carmamo/Avionics-FYCUS/Hardware/KiCAD_Libs/RM-VT02/3D/RM-VT02.stp

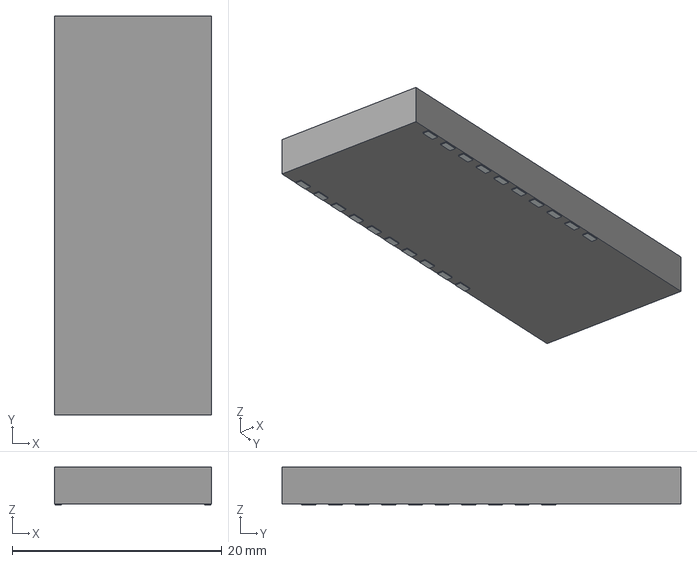
[picture p23: CAD file, 2023-10-23]
Hardware/KiCAD_Libs/RM-VT02/3D/RM-VT02.stp
15.0 x 38.0 x 3.60 mm
Pins
