carmamo/Avionics-FYCUS/Hardware/KiCAD_Libs/RQ3G100GNTB/3D/RQ3G100GNTB.stp

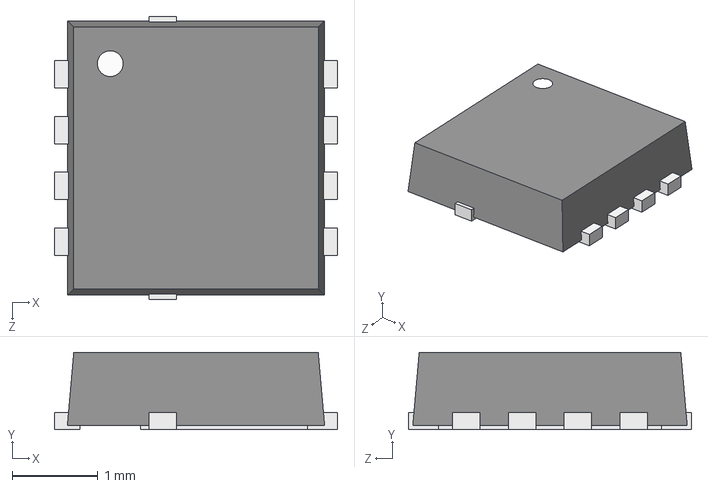
[picture p24: CAD file, 2023-10-23]
Hardware/KiCAD_Libs/RQ3G100GNTB/3D/RQ3G100GNTB.stp
3.30 x 0.9 x 3.30 mm
