carmamo/Avionics-FYCUS/Hardware/KiCAD_Libs/SSW-120-03-G-D/3D/SSW-120-03-G-D.stp

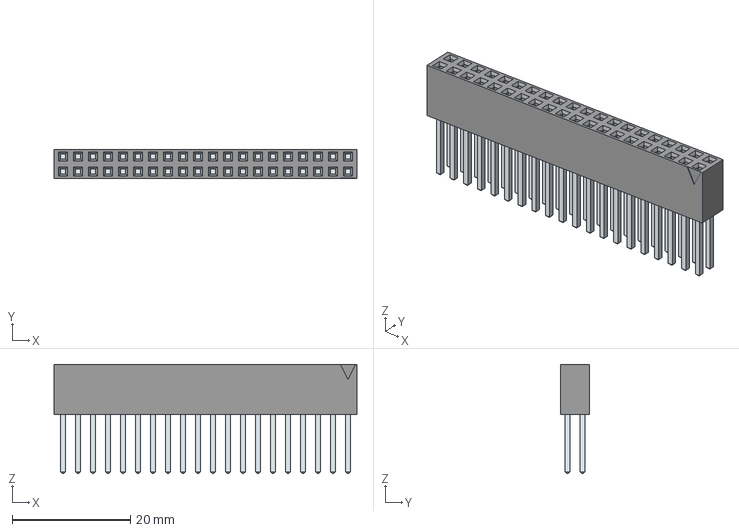
[picture p25: CAD file, 2023-10-23]
Hardware/KiCAD_Libs/SSW-120-03-G-D/3D/SSW-120-03-G-D.stp
51.3 x 4.95 x 18.5 mm
LeadsArray
