carmamo/Avionics-FYCUS/Hardware/KiCAD_Libs/STM32L431RCT6/3D/STM32L431RCT6.stp

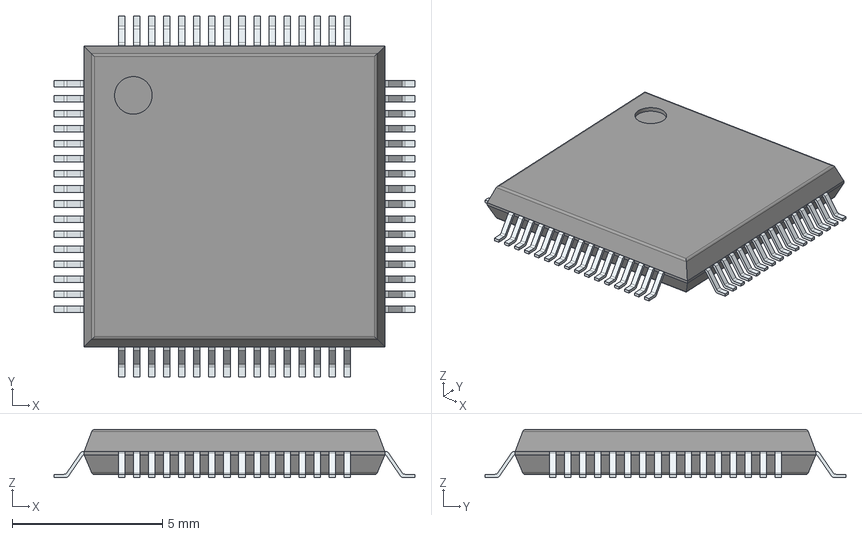
[picture p26: CAD file, 2023-10-23]
Hardware/KiCAD_Libs/STM32L431RCT6/3D/STM32L431RCT6.stp
12.0 x 12.0 x 1.60 mm
PinsArrayLR
PinsArrayTB
