carmamo/Avionics-FYCUS/Hardware/KiCAD_Libs/USB4125-GF-A-0190/3D/USB4125-GF-A-0190.stp

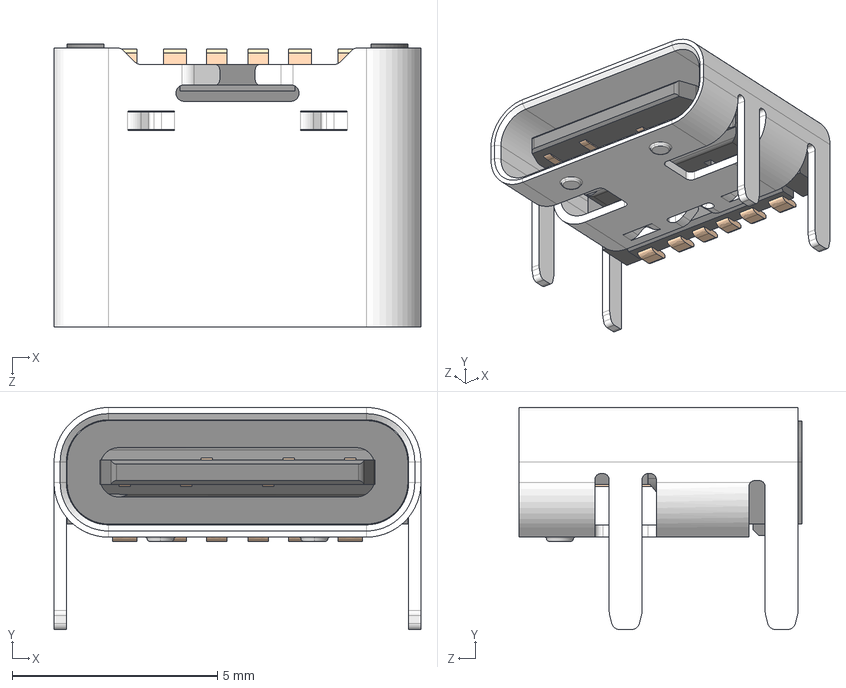
[picture p27: CAD file, 2023-10-23]
Hardware/KiCAD_Libs/USB4125-GF-A-0190/3D/USB4125-GF-A-0190.stp
8.94 x 5.41 x 6.90 mm
