carmamo/Avionics-FYCUS/Hardware/KiCAD_Libs/XAL1060-222MEB/3D/XAL1060-222MEB.stp

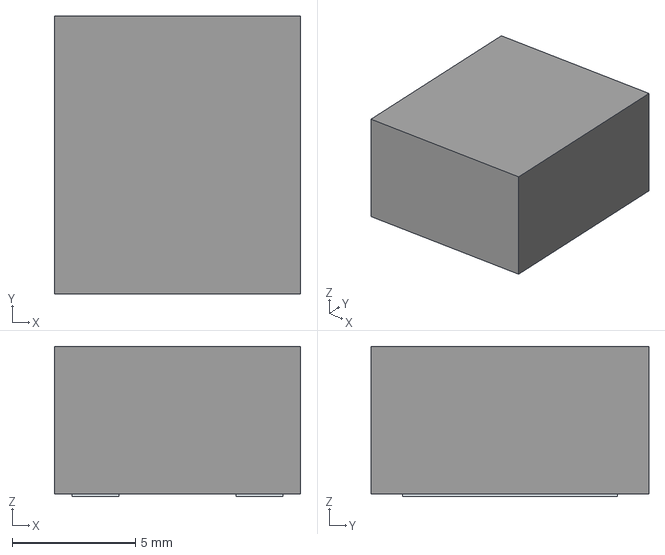
[picture p28: CAD file, 2023-10-23]
Hardware/KiCAD_Libs/XAL1060-222MEB/3D/XAL1060-222MEB.stp
10.0 x 11.3 x 6.10 mm
Pins
