carmamo/Avionics-FYCUS/Hardware/EPS/production/EPS-F_Cu.dxf

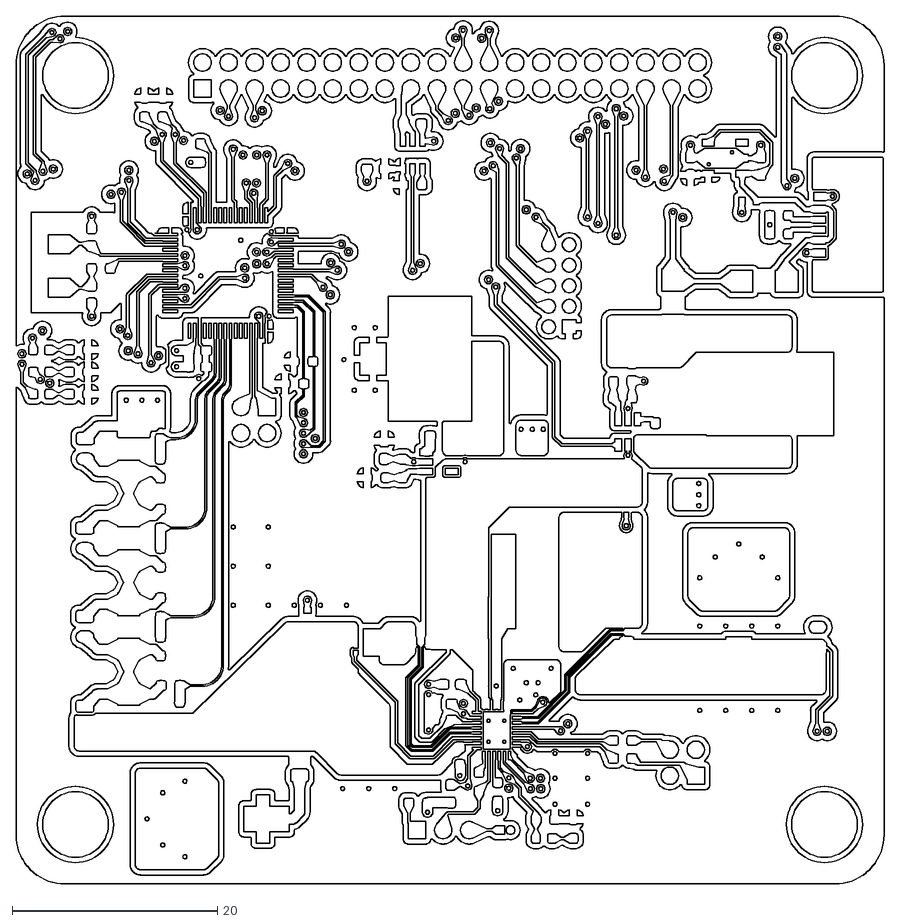
[picture p29: CAD file, 2023-10-23]
Hardware/EPS/production/EPS-F_Cu.dxf
84.6 x 84.6
