carmamo/Avionics-FYCUS/Hardware/EPS/production/EPS-Edge_Cuts.dxf

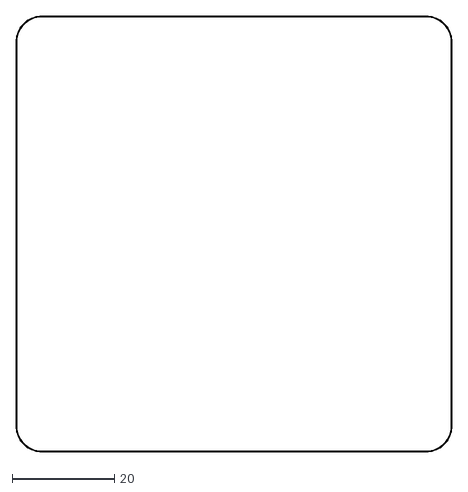
[picture p30: CAD file, 2023-10-23]
Hardware/EPS/production/EPS-Edge_Cuts.dxf
85.1 x 85.1
