carmamo/Avionics-FYCUS/Hardware/EPS/production/EPS-GND1_Cu.dxf

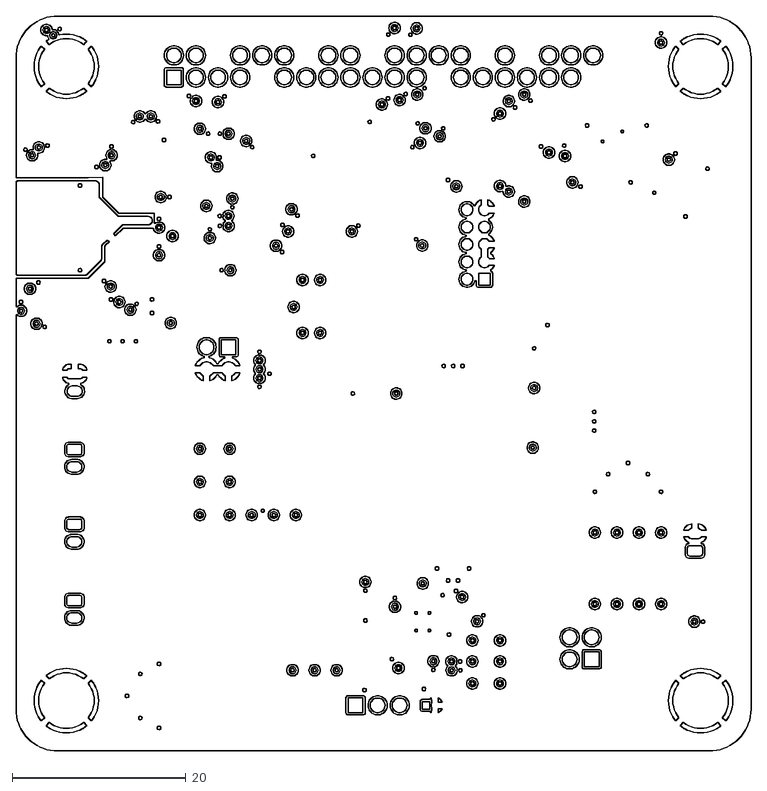
[picture p31: CAD file, 2023-10-23]
Hardware/EPS/production/EPS-GND1_Cu.dxf
84.6 x 84.6
