carmamo/Avionics-FYCUS/Hardware/EPS/production/EPS-B_Cu.dxf

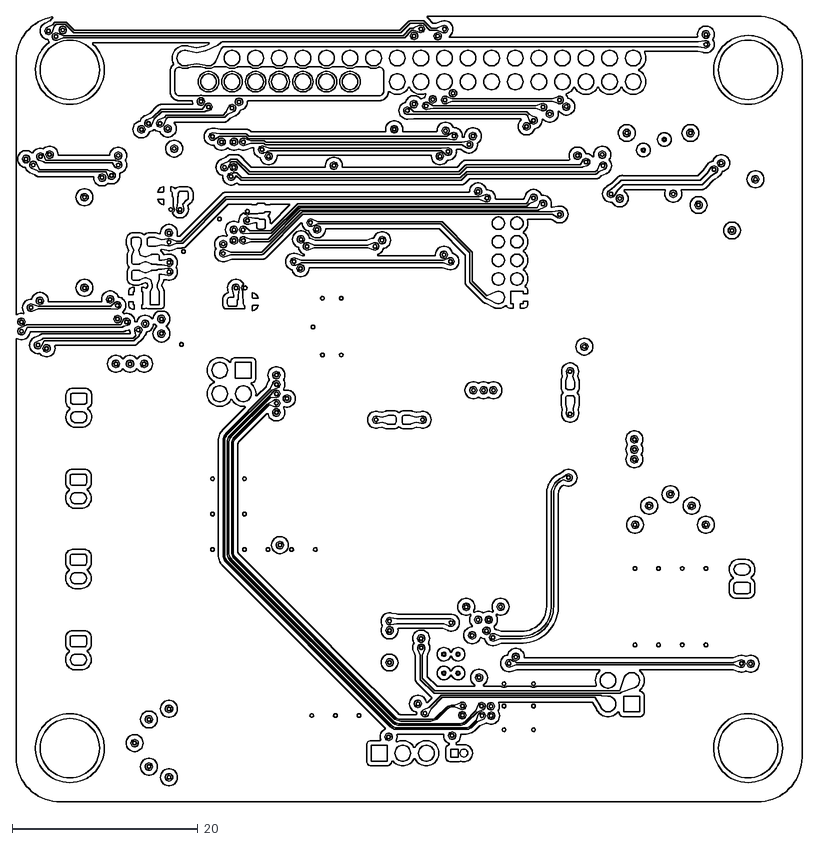
[picture p32: CAD file, 2023-10-23]
Hardware/EPS/production/EPS-B_Cu.dxf
84.6 x 84.6
