carmamo/Avionics-FYCUS/Firmware/EPS_Firmware/Core/Inc/main.h

#define LED_R_Pin GPIO_PIN_1
#define LED_R_GPIO_Port GPIOC
#define LED_G_Pin GPIO_PIN_2
#define LED_G_GPIO_Port GPIOC
#define LED_YL_Pin GPIO_PIN_3
#define LED_YL_GPIO_Port GPIOC
#define SBMALERT_Pin GPIO_PIN_15
#define SBMALERT_GPIO_Port GPIOB
#define EN_5V_Pin GPIO_PIN_9
#define EN_5V_GPIO_Port GPIOC
#define EN_3V3_Pin GPIO_PIN_8
#define EN_3V3_GPIO_Port GPIOA
